devakumar18dk-spec/eSim_PCB_Design_Project_Files/enhancedpowersupplyesp32/images/3d_image.png

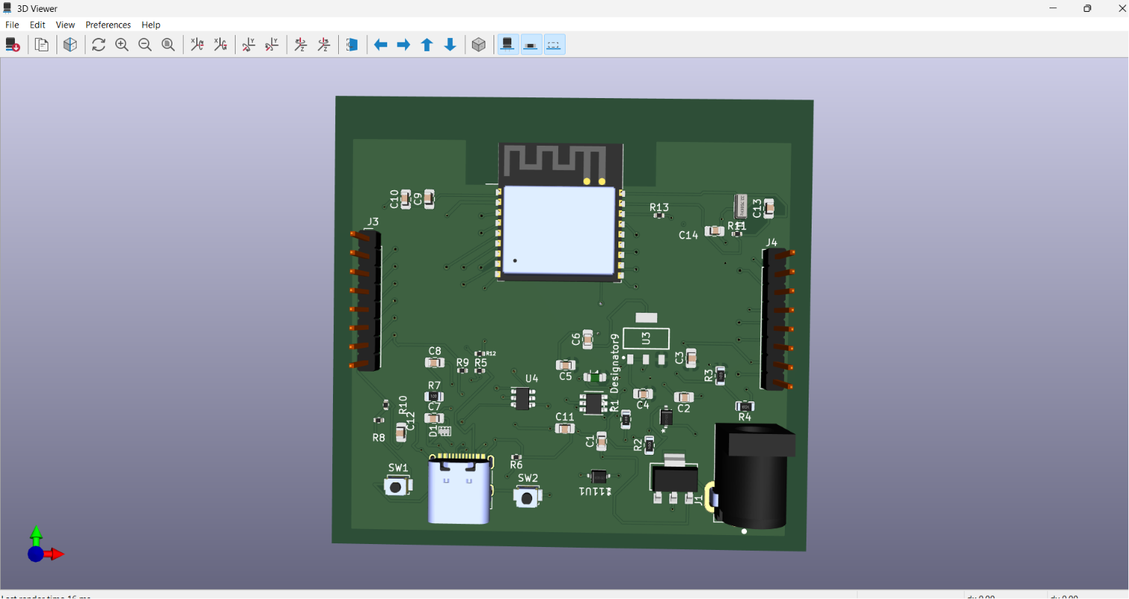
enhancedpowersupplyesp32/images/3d_image.png
