devakumar18dk-spec/eSim_PCB_Design_Project_Files/enhancedpowersupplyesp32/images/ESP32_C3_WROOM_02_N4.png

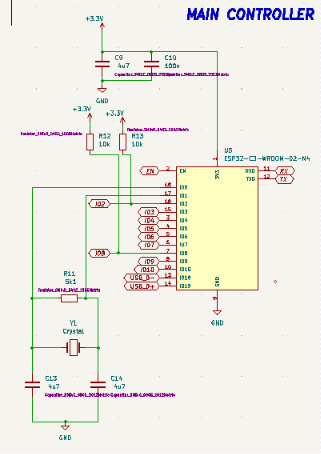
enhancedpowersupplyesp32/images/ESP32_C3_WROOM_02_N4.png
