devakumar18dk-spec/eSim_PCB_Design_Project_Files/enhancedpowersupplyesp32/images/images (1).jpg

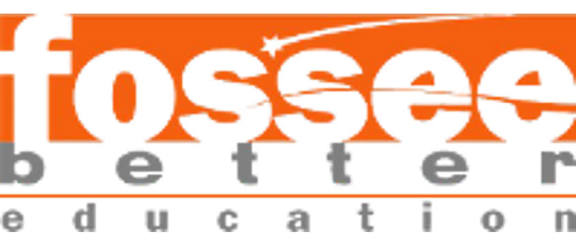
enhancedpowersupplyesp32/images/images (1).jpg
