devakumar18dk-spec/eSim_PCB_Design_Project_Files/enhancedpowersupplyesp32/images/inputpower(24-7)V_5V buck boost_3V3 LDO.png

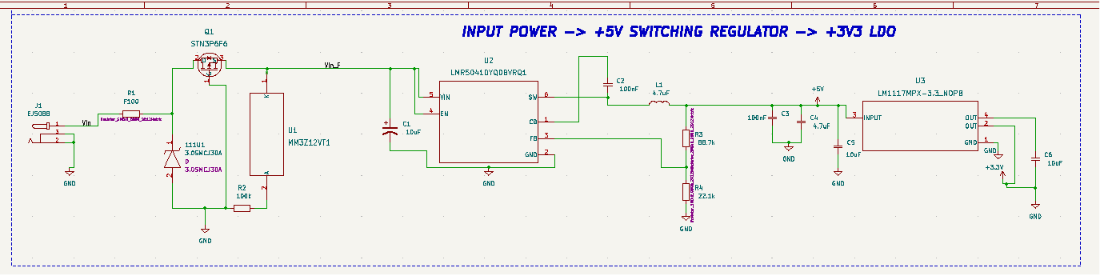
enhancedpowersupplyesp32/images/inputpower(24-7)V_5V buck boost_3V3 LDO.png
