devakumar18dk-spec/eSim_PCB_Design_Project_Files/enhancedpowersupplyesp32/images/USB_Connection_procetion.png

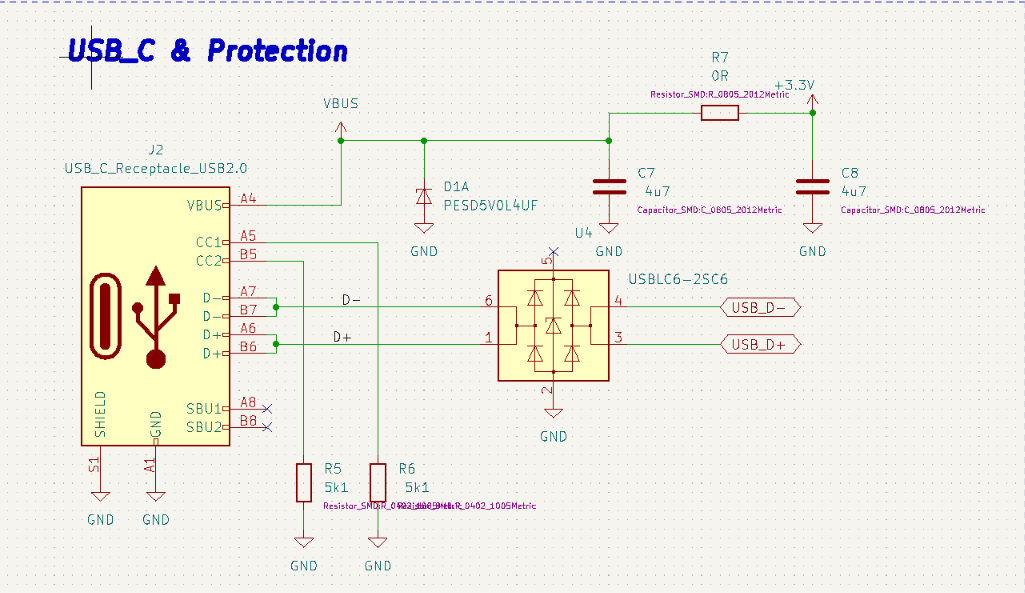
enhancedpowersupplyesp32/images/USB_Connection_procetion.png
