devakumar18dk-spec/eSim_PCB_Design_Project_Files/enhancedpowersupplyesp32/images/boardsetup.png

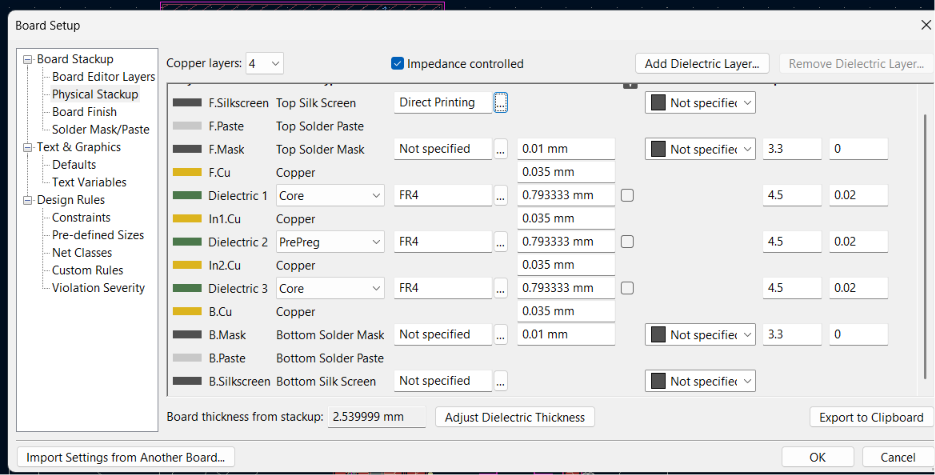
enhancedpowersupplyesp32/images/boardsetup.png
